Wilko01/Air_Quality_Meter/Images/Air_quality_meter03.jpg

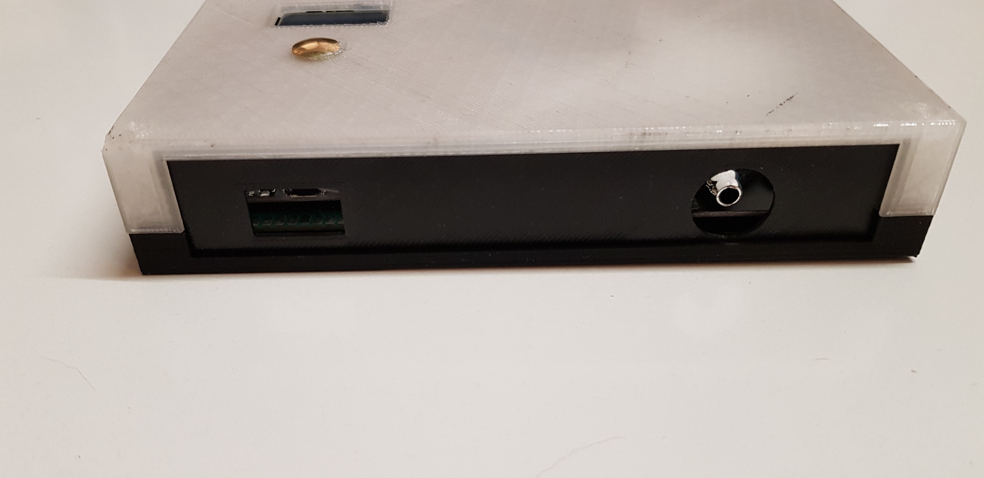
Images/Air_quality_meter03.jpg
