Wilko01/Air_Quality_Meter/Images/Air_quality_meter05.jpg

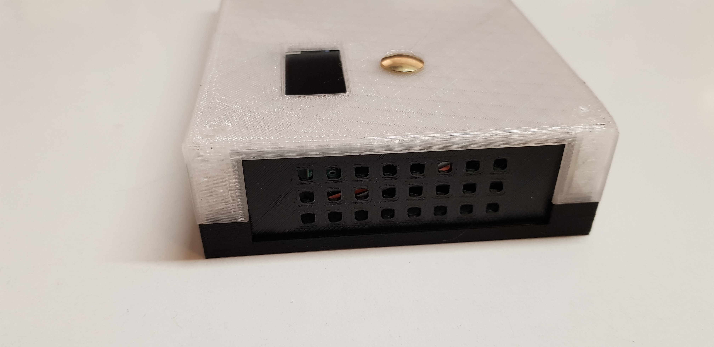
Images/Air_quality_meter05.jpg
